toby-l-baker/embedded-project/hardware/Manufacturing Files/Front_Fork.stl

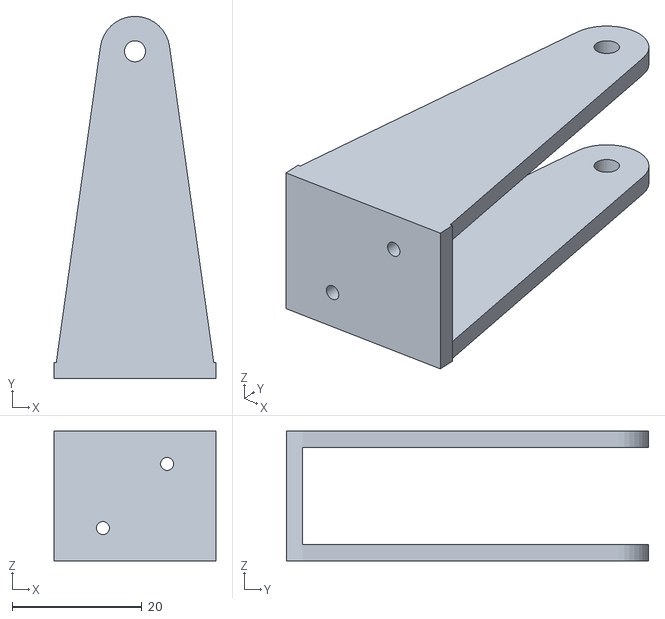
[picture p15: CAD file, 2019-11-19]
hardware/Manufacturing Files/Front_Fork.stl
25.0 x 55.9 x 20.0
