toby-l-baker/embedded-project/hardware/Flattened_Base.SLDPRT

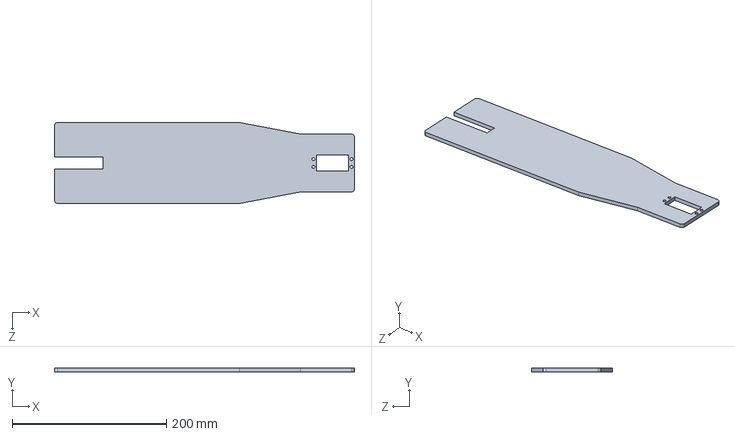
[picture p16: CAD file, 2019-11-19]
hardware/Flattened_Base.SLDPRT
389.0 x 5.00 x 105.0 mm
