toby-l-baker/embedded-project/hardware/Manufacturing Files/Servo_Front_Fork_Connector.stl

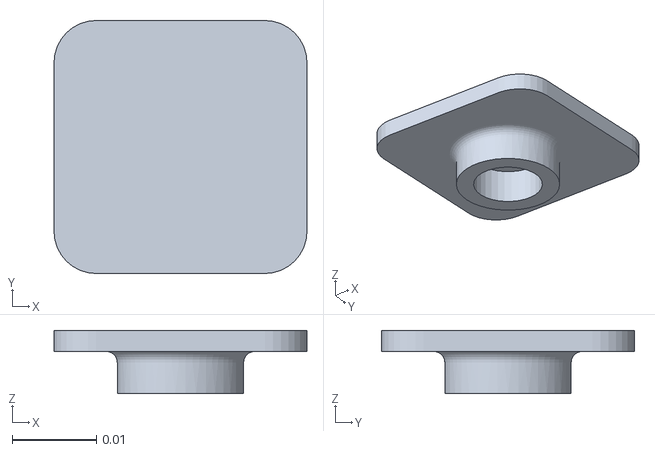
[picture p17: CAD file, 2019-11-07]
hardware/Manufacturing Files/Servo_Front_Fork_Connector.stl
0.03 x 0.03 x 0.0075
