toby-l-baker/embedded-project/hardware/Manufacturing Files/Flywheel_coupler.stl

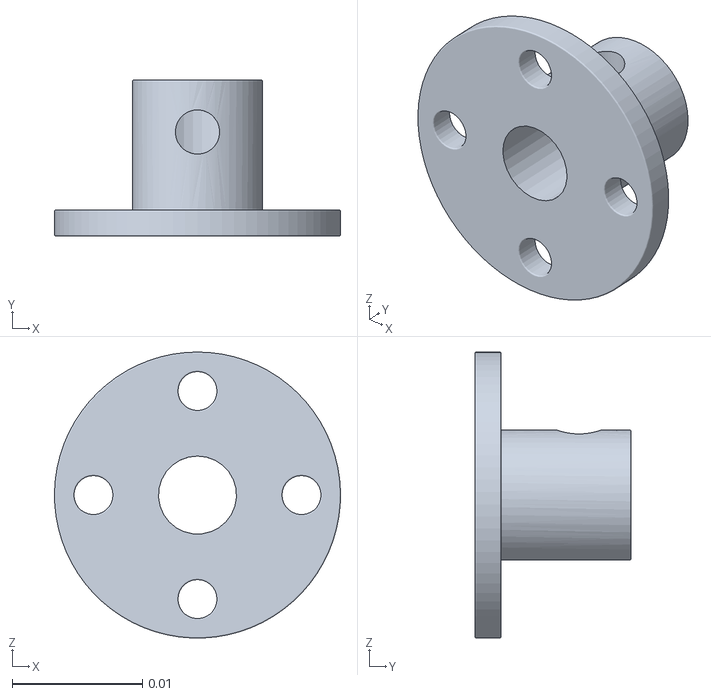
[picture p18: CAD file, 2019-11-07]
hardware/Manufacturing Files/Flywheel_coupler.stl
0.022 x 0.012 x 0.022
