toby-l-baker/embedded-project/hardware/Bike_Base.SLDPRT

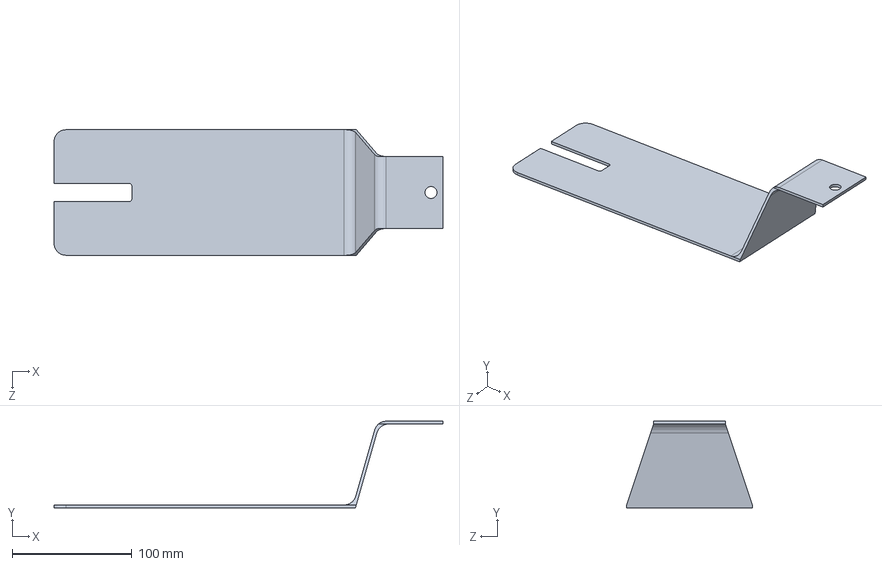
[picture p19: CAD file, 2019-11-06]
hardware/Bike_Base.SLDPRT
325.0 x 72.5 x 105.0 mm
