toby-l-baker/embedded-project/hardware/Manufacturing Files/Bike_Base.stl

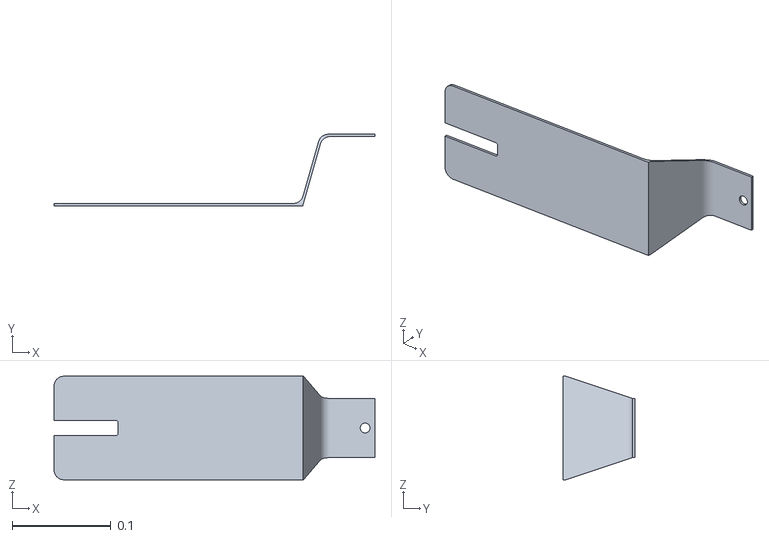
[picture p20: CAD file, 2019-11-07]
hardware/Manufacturing Files/Bike_Base.stl
0.325 x 0.0725 x 0.105
