toby-l-baker/embedded-project/hardware/Flywheel_Motor.SLDPRT

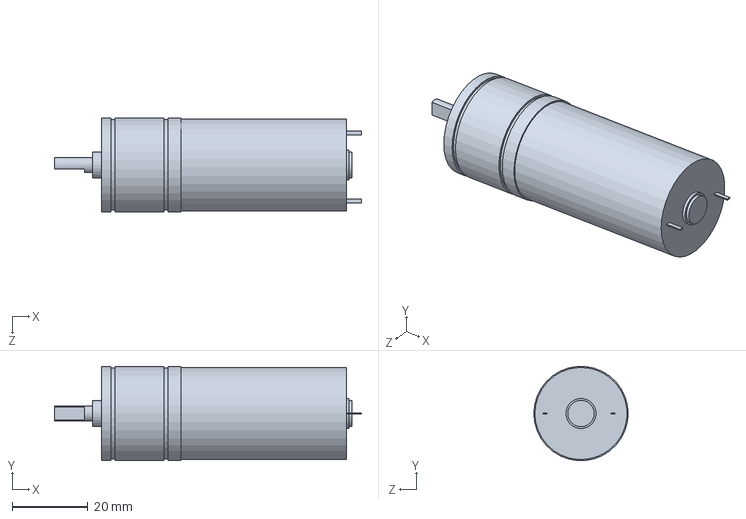
[picture p21: CAD file, 2019-11-06]
hardware/Flywheel_Motor.SLDPRT
81.3 x 24.9 x 25.0 mm
