toby-l-baker/embedded-project/hardware/Manufacturing Files/Flywheel_Motor_Holder.stl

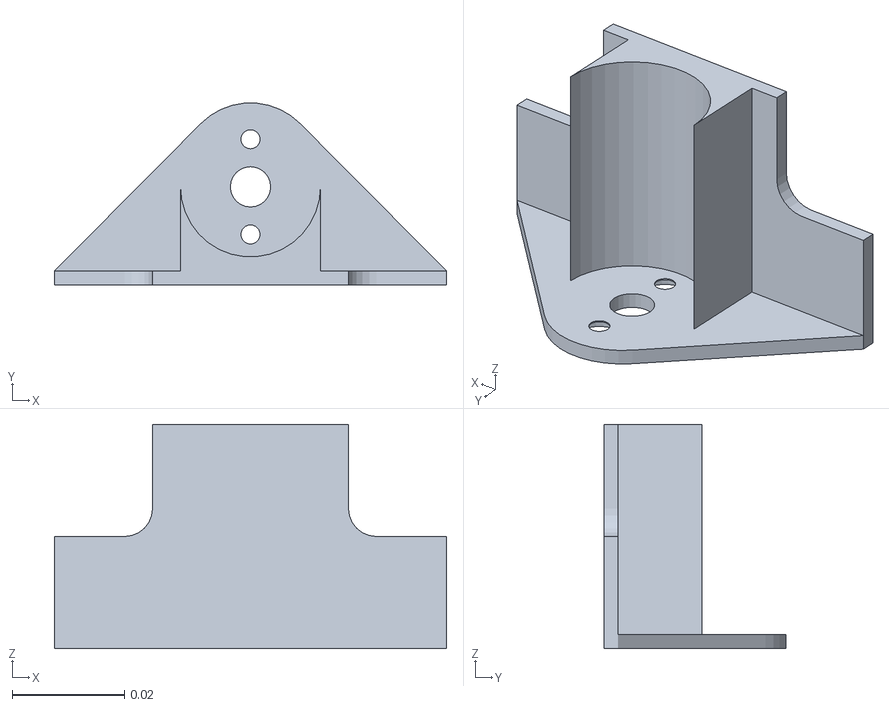
[picture p22: CAD file, 2019-11-07]
hardware/Manufacturing Files/Flywheel_Motor_Holder.stl
0.07 x 0.0325 x 0.04
