toby-l-baker/embedded-project/hardware/L298N.SLDPRT

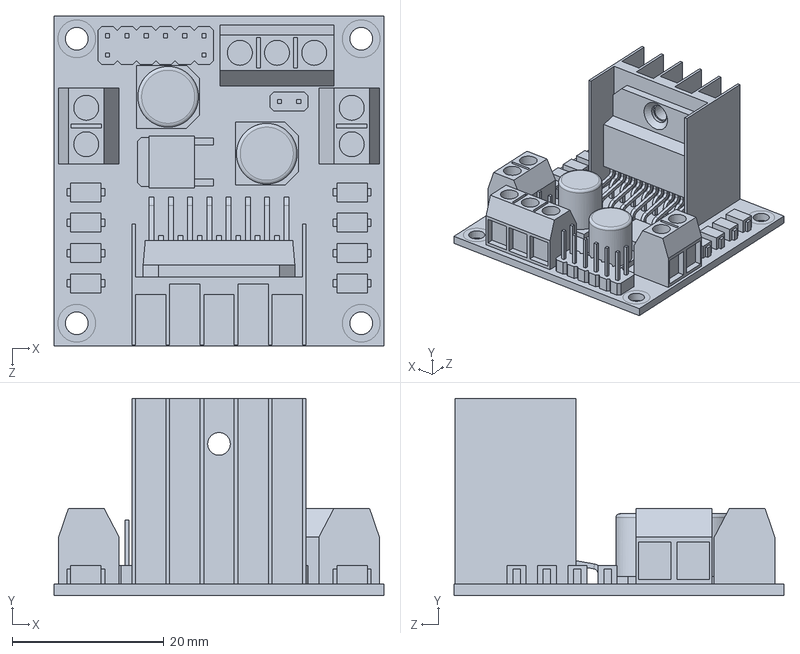
[picture p23: CAD file, 2019-11-06]
hardware/L298N.SLDPRT
43.5 x 26.0 x 43.5 mm
