toby-l-baker/embedded-project/hardware/Manufacturing Files/Flywheel_Motor_Holder_Base.stl

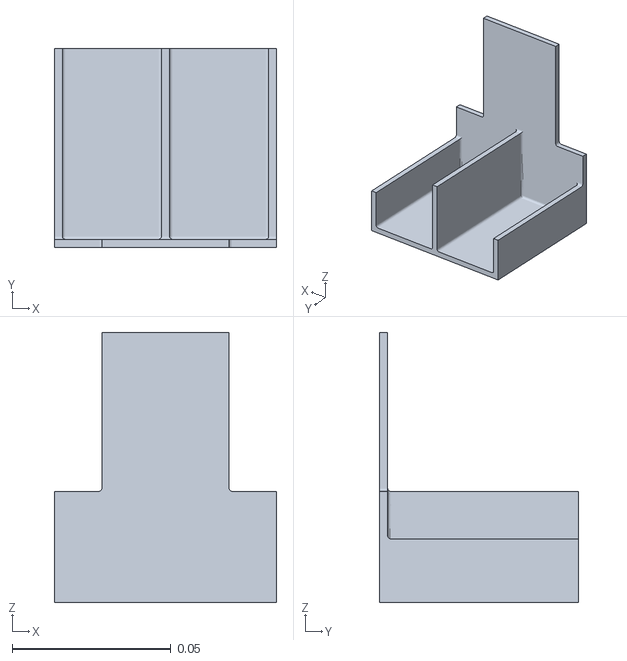
[picture p24: CAD file, 2019-11-07]
hardware/Manufacturing Files/Flywheel_Motor_Holder_Base.stl
0.07 x 0.0625 x 0.085
