toby-l-baker/embedded-project/hardware/Buckler_Place_Holder.SLDPRT

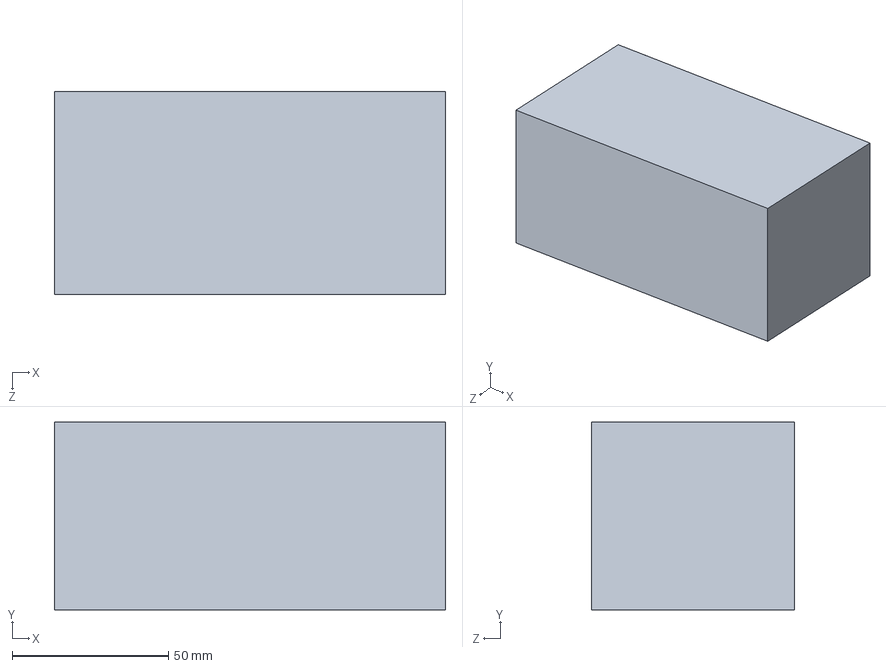
[picture p25: CAD file, 2019-11-06]
hardware/Buckler_Place_Holder.SLDPRT
125.0 x 60.0 x 65.0 mm
