toby-l-baker/embedded-project/hardware/Flywheel_Motor_Holder.SLDPRT

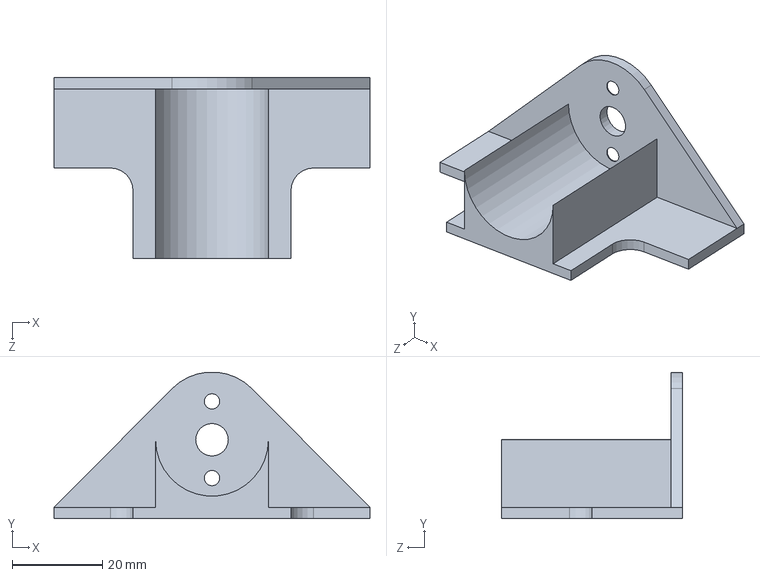
[picture p26: CAD file, 2019-11-06]
hardware/Flywheel_Motor_Holder.SLDPRT
70.0 x 32.5 x 40.0 mm
