toby-l-baker/embedded-project/hardware/Flywheel_Motor_Holder_Base.SLDPRT

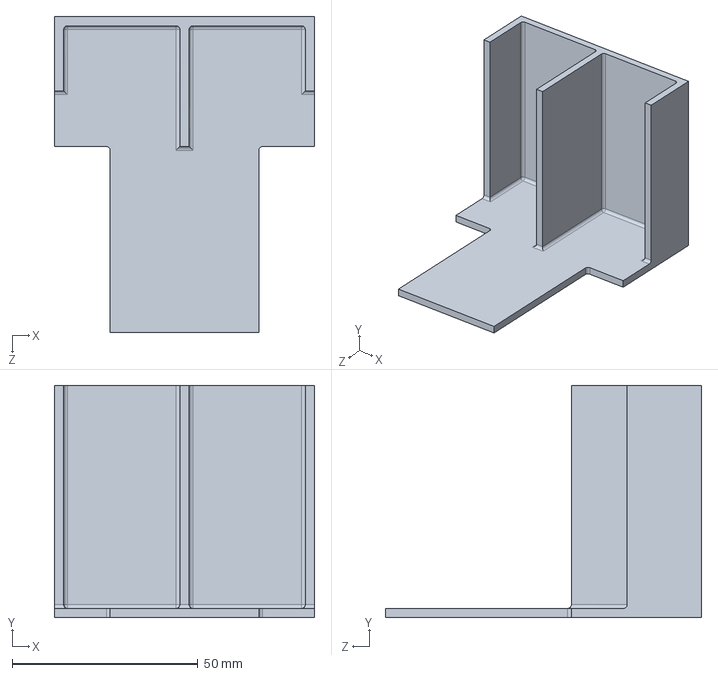
[picture p27: CAD file, 2019-11-06]
hardware/Flywheel_Motor_Holder_Base.SLDPRT
70.0 x 62.5 x 85.0 mm
