toby-l-baker/embedded-project/hardware/Servo_Front_Fork_Connector.SLDPRT

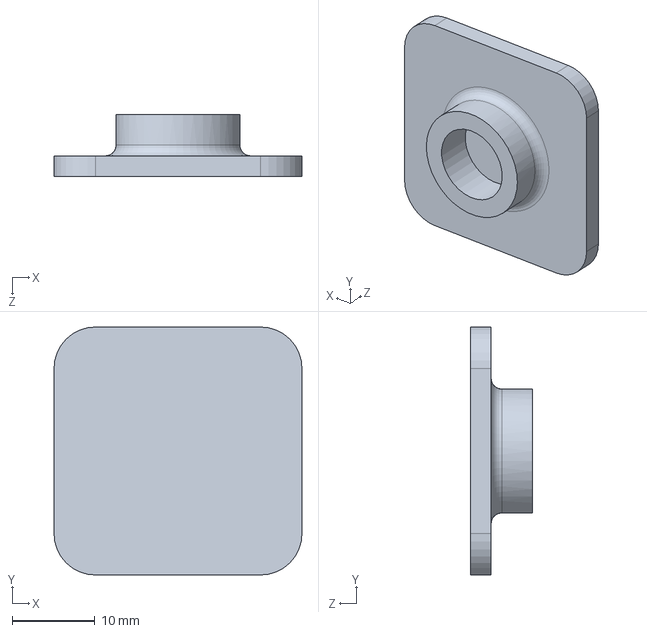
[picture p28: CAD file, 2019-11-06]
hardware/Servo_Front_Fork_Connector.SLDPRT
30.0 x 30.0 x 7.50 mm
