toby-l-baker/embedded-project/hardware/Servo_Plate.SLDPRT

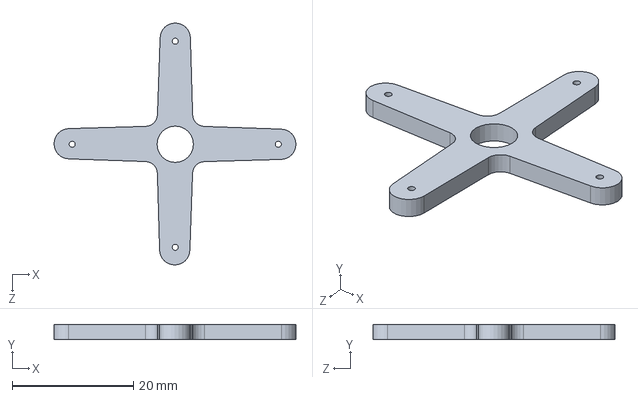
[picture p29: CAD file, 2019-11-06]
hardware/Servo_Plate.SLDPRT
39.9 x 2.50 x 39.9 mm
