toby-l-baker/embedded-project/hardware/servo_motor.SLDPRT

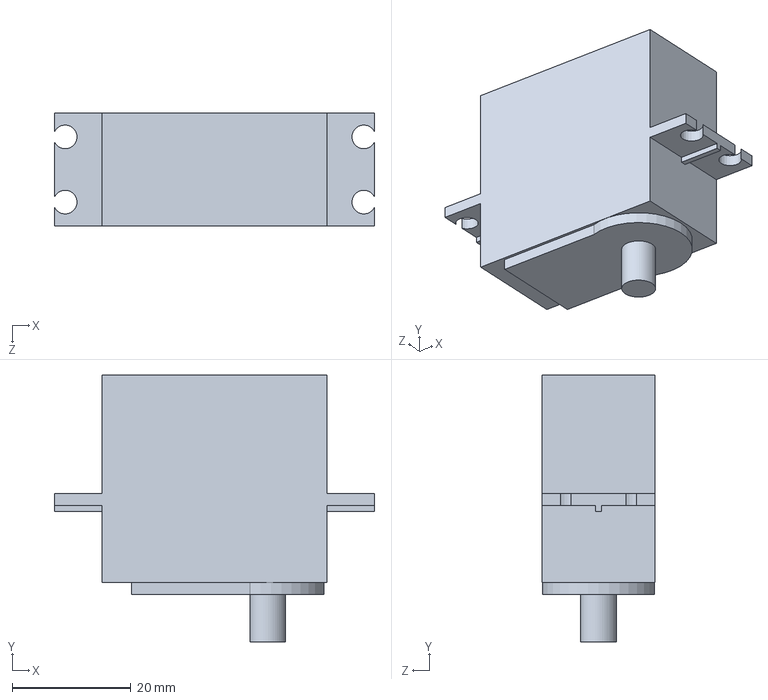
[picture p30: CAD file, 2019-11-06]
hardware/servo_motor.SLDPRT
54.0 x 45.0 x 19.0 mm
