toby-l-baker/embedded-project/hardware/Flywheel_coupler.SLDPRT

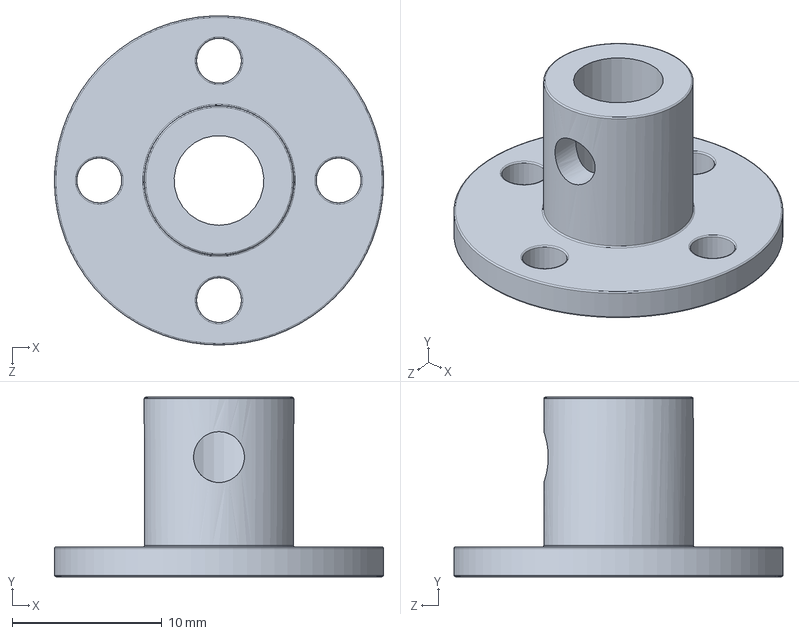
[picture p31: CAD file, 2019-11-06]
hardware/Flywheel_coupler.SLDPRT
22.0 x 12.0 x 22.0 mm
