toby-l-baker/embedded-project/hardware/Flywheel.SLDPRT

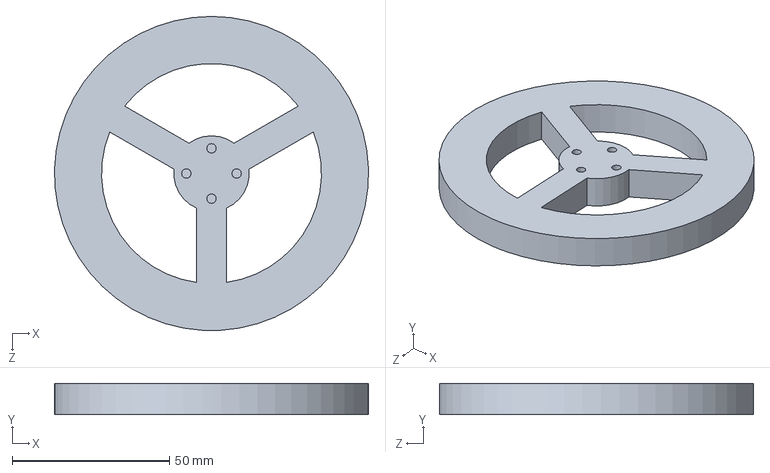
[picture p32: CAD file, 2019-11-06]
hardware/Flywheel.SLDPRT
100.0 x 10.0 x 100.0 mm
