toby-l-baker/embedded-project/hardware/Basic_Wheel_Model.SLDPRT

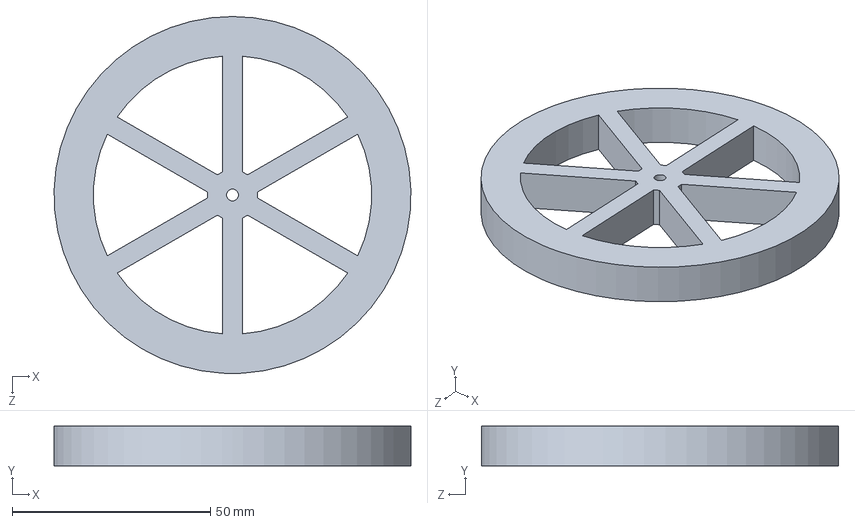
[picture p33: CAD file, 2019-11-05]
hardware/Basic_Wheel_Model.SLDPRT
90.0 x 10.0 x 90.0 mm
