toby-l-baker/embedded-project/hardware/Drive_Motor.SLDPRT

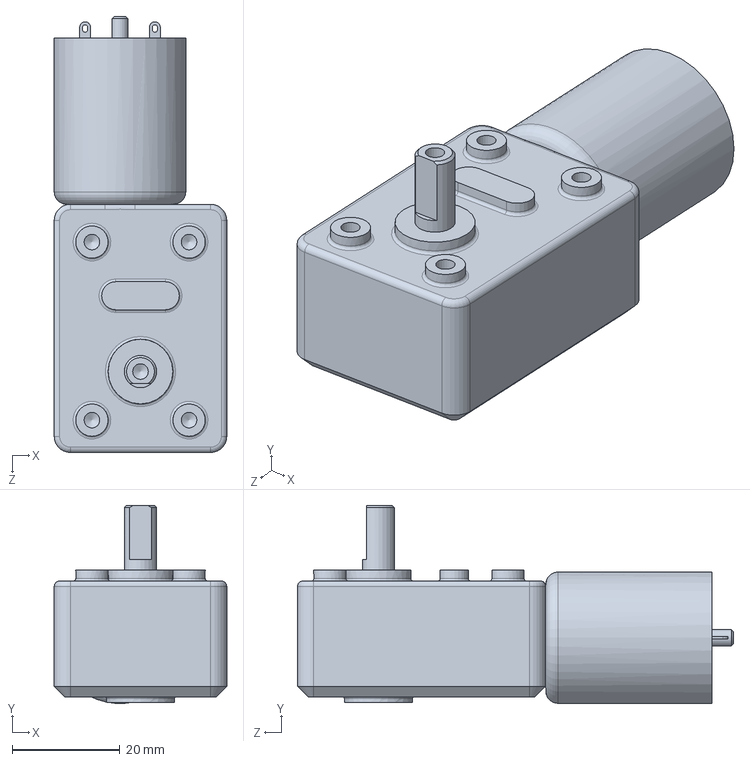
[picture p34: CAD file, 2019-11-05]
hardware/Drive_Motor.SLDPRT
32.0 x 36.7 x 80.8 mm
