toby-l-baker/embedded-project/software/apps/final_implementation/ble_receiver.c

#include "ble_receiver.h"

simple_ble_app_t* simple_ble_app = NULL;

// Intervals for advertising and connections
static simple_ble_config_t ble_config = {
        // c0:98:e5:49:xx:xx
        .platform_id       = 0x49,    // used as 4th octect in device BLE address
        .device_id         = 0x000b, // TODO: replace with your lab bench number
        .adv_name          = "SickestBikeEver", // used in advertisements if there is room
        .adv_interval      = MSEC_TO_UNITS(1000, UNIT_0_625_MS),
        .min_conn_interval = MSEC_TO_UNITS(100, UNIT_1_25_MS),
        .max_conn_interval = MSEC_TO_UNITS(200, UNIT_1_25_MS),
};
//4607eda0-f65e-4d59-a9ff-84420d87a4ca
//stored in little endian
static simple_ble_service_t bike_srv = {{
    .uuid128 = {0xca,0xa4,0x87,0x0d,0x42,0x84,0xff,0xA9,
                0x59,0x4D,0x5e,0xf6,0xa0,0xed,0x07,0x46}
}};

static simple_ble_char_t manual_char = {.uuid16 = 0xeda1};
bool manual_control=0;

static simple_ble_char_t power_char = {.uuid16 = 0xeda2};
bool power=0;

static simple_ble_char_t drive_char = {.uuid16 = 0xeda3};
int8_t drive_speed=0;

static simple_ble_char_t turn_char = {.uuid16 = 0xeda4};
int8_t turn_angle=0;

static simple_ble_char_t path_len_char = {.uuid16 = 0xeda5};
uint8_t path_len; // will be range of 0 to 255 cm

static simple_ble_char_t path_angle_char = {.uuid16 = 0xeda6};
int8_t path_angle; //will be 0 to 255, need to do 360/255 * path_angle to get degrees

void ble_evt_write(ble_evt_t const* p_ble_evt) {
    if (simple_ble_is_char_event(p_ble_evt, &manual_char)) {
      if (manual_control) { // set bike state to manual
        bike_state = MANUAL;
      } else {
        bike_state = AUTONOMOUS;
      }
    } else if (simple_ble_is_char_event(p_ble_evt, &power_char)) {
      if (power) {
        bike_state = MANUAL;
      } else {
        bike_state = OFF;
      }
    } else if (simple_ble_is_char_event(p_ble_evt, &path_len_char)) {
      nav_complete = false;
      path_len_received = true;
      destination_set = false;
    } else if (simple_ble_is_char_event(p_ble_evt, &path_angle_char)) {
      nav_complete = false;
      path_angle_received = true;
      destination_set = false;
    }
}

void init_ble_receiver(void){
  // Setup BLE
	simple_ble_app = simple_ble_init(&ble_config);

	simple_ble_add_service(&bike_srv);

	// Start Advertising
	simple_ble_adv_only_name();

	simple_ble_add_characteristic(1, 1, 0, 0,
	  sizeof(manual_control), (uint8_t*)&manual_control,
	  &bike_srv, &manual_char);

	simple_ble_add_characteristic(1, 1, 0, 0,
	  sizeof(power), (uint8_t*)&power,
	  &bike_srv, &power_char);

	simple_ble_add_characteristic(1, 1, 0, 0,
	  sizeof(drive_speed), (uint8_t*)&drive_speed,
	  &bike_srv, &drive_char);

	simple_ble_add_characteristic(1, 1, 0, 0,
	  sizeof(turn_angle), (uint8_t*)&turn_angle,
	  &bike_srv, &turn_char);

	simple_ble_add_characteristic(1, 1, 0, 0,
	  sizeof(path_len), (uint8_t*)&path_len,
	  &bike_srv, &path_len_char);

  simple_ble_add_characteristic(1, 1, 0, 0,
	  sizeof(path_angle), (uint8_t*)&path_angle,
	  &bike_srv, &path_angle_char);

	printf("BLE Receiver Initialized.\n");
}
