toby-l-baker/embedded-project/software/apps/final_implementation/timer_module.c

#include "timer_module.h"

static uint32_t recorded_vals[NUM_LOOPS] = {0};
static int current_idx = 0;

static uint32_t start_val = 0;
static uint32_t end_val = 0;


// nrfx_timer_t TIMER = NRFX_TIMER_INSTANCE(4);
float delta_time(float t1, float t2){
	// returns time difference in seconds
	return (t1 - t2);
}

void start_timer(){
	start_val = get_timer_value();
	// printf("%u\n", start_val);
}

void end_timer(){
	end_val = get_timer_value();
	// printf("%u\n", end_val);
	recorded_vals[current_idx++] = end_val - start_val;

	start_val = end_val = 0;
}

float timestamp(){
	// printf("In timestamp: %f\n", get_timer_value());

	return (float)(get_timer_value()) ;
}

uint32_t get_timer_value() {
	NRF_TIMER4->TASKS_CAPTURE[1] |= 1;
	uint32_t timer_value = NRF_TIMER4->CC[1];
	// NRF_TIMER4->TASKS_CAPTURE[1] ;
	return timer_value;
}

float convert_to_secs(uint32_t time_){
	return (float)(time_ * PRESCALE_CONV);
}

void print_timer_vals(){
	for (int i =0; i < NUM_LOOPS; i++){
		printf("%f, ", (float)(recorded_vals[i]* PRESCALE_CONV));
	}
}

void init_timer_module() {

	NRF_TIMER4->BITMODE = 3;
	NRF_TIMER4->MODE = 0;
	NRF_TIMER4->PRESCALER = 4; // Read at 16 Mhz / 16 = 1MHz
	NRF_TIMER4->TASKS_CLEAR = 1; //Set TASKS_CLEAR
	NRF_TIMER4->TASKS_START = 1; //Set TASKS_START
	NRF_TIMER4->INTENSET = 1<<16; //Enable interrupts for CC[0]
	// NVIC_EnableIRQ(TIMER4_IRQn);
	printf("Timer module initialized using TIMER%i.\n", TIMER_MODULE_TIMER);
}
