toby-l-baker/embedded-project/software/apps/timer/virtual_timer.h

#pragma once

#include "nrf.h"
// Read the current value of the hardware timer counter
// Returns the counter value
uint32_t read_timer(void);

// Initialize the timer peripheral
void virtual_timer_init(void);
